P-DoxQuad/Bluetooth-Accessibility-Switch-Interface/Firmware/_32u4_BLE_SwitchClick_v1/TimeWait.h

/*
Name:     TimeWait.h
Created:  04/15/2017 1:35:00 PM
Author:   Michael Dzura
Version: 1.0

Declaration Of Function
*/

#ifndef TIMEWAIT_H
#define TIMEWAIT_H

#include "Arduino.h"

void wait(long interval);

#endif
